mael-lukas/2425_Maker_MiniatureHomeControl/Media/Project pictures/pic2.jpeg

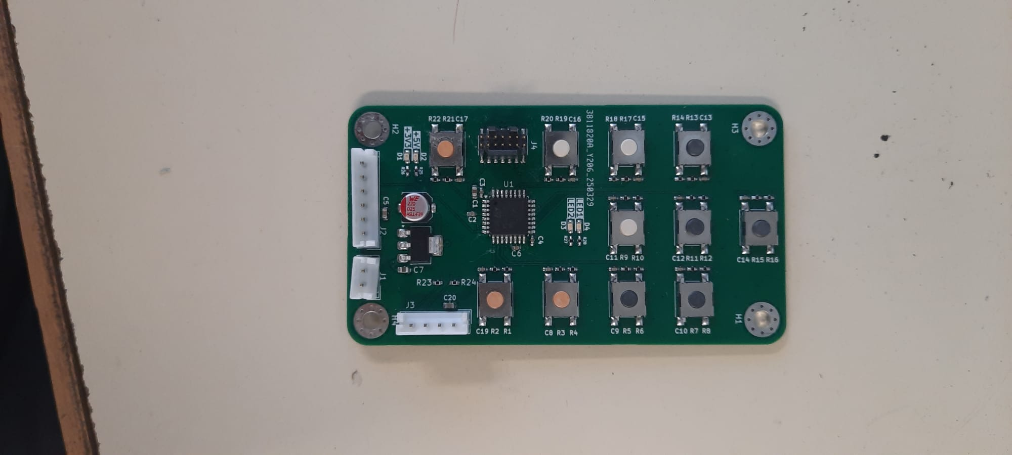
Media/Project pictures/pic2.jpeg
