mael-lukas/2425_Maker_MiniatureHomeControl/Media/Project pictures/pic14.png

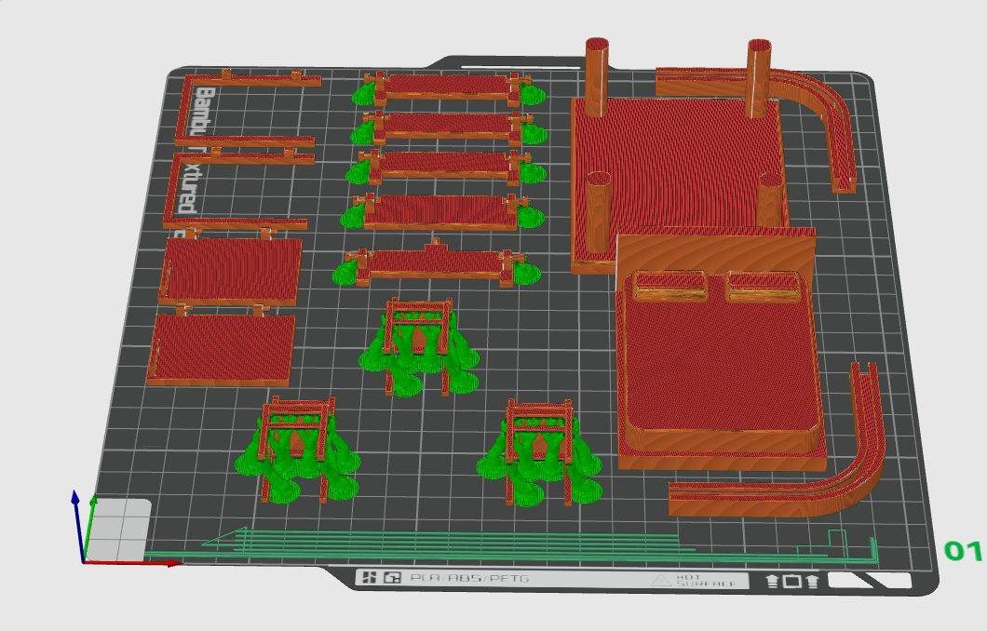
Media/Project pictures/pic14.png
