mael-lukas/2425_Maker_MiniatureHomeControl/Media/Project pictures/pic17.png

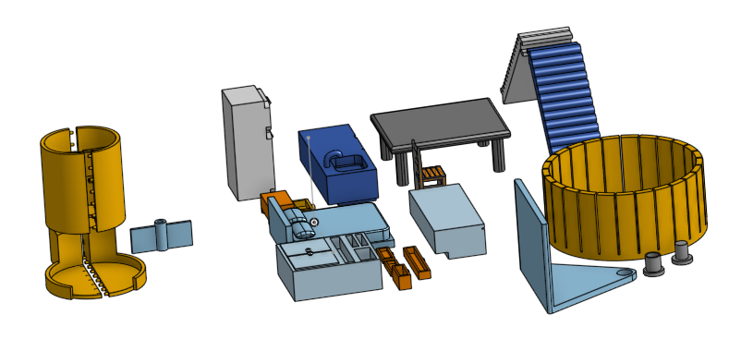
Media/Project pictures/pic17.png
