mael-lukas/2425_Maker_MiniatureHomeControl/Media/Project pictures/pic.jpeg

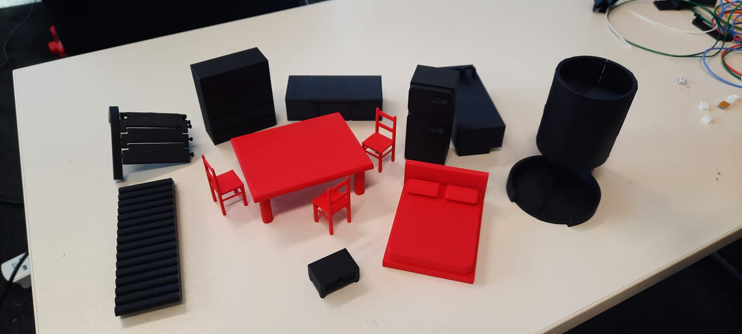
Media/Project pictures/pic.jpeg
