mael-lukas/2425_Maker_MiniatureHomeControl/Project Management/archi diagram.jpg

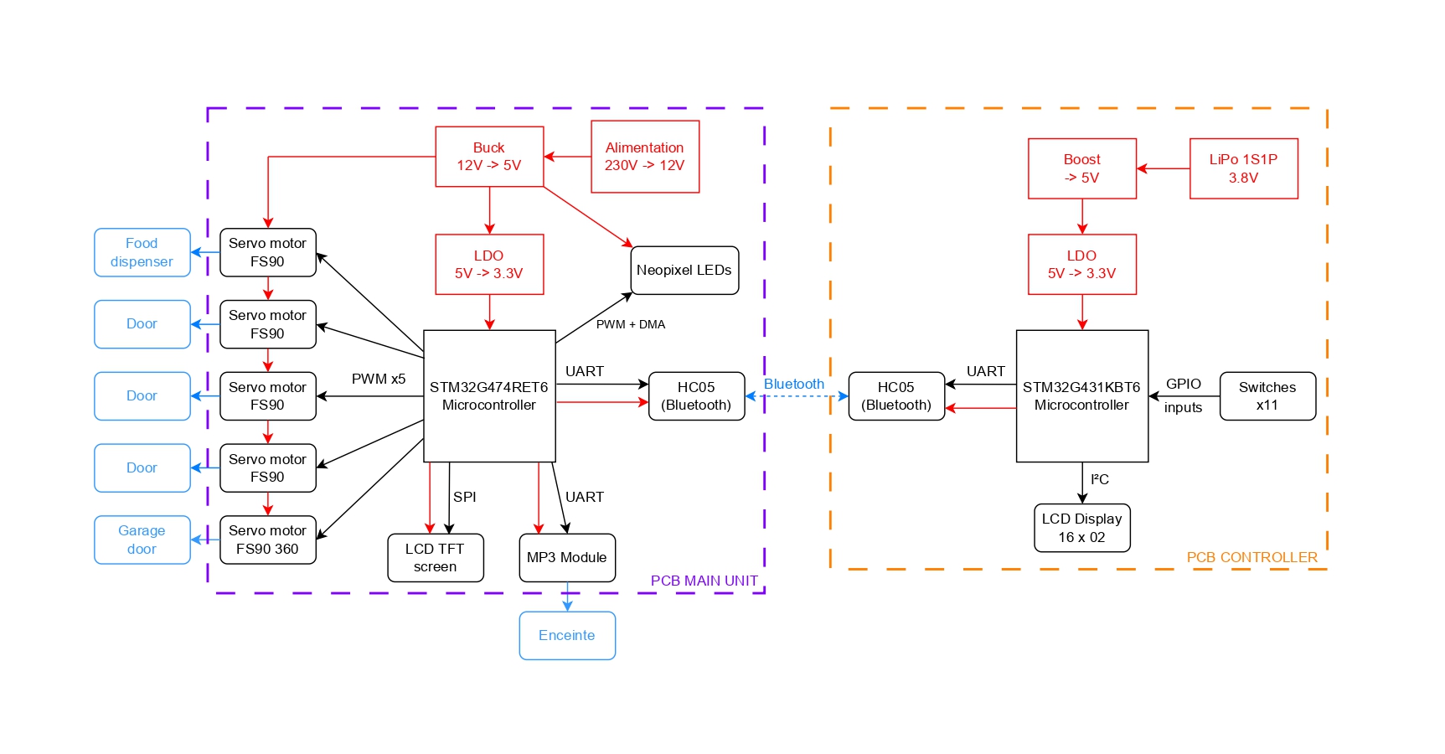
Project Management/archi diagram.jpg
