mael-lukas/2425_Maker_MiniatureHomeControl/CAD/food_3.stl

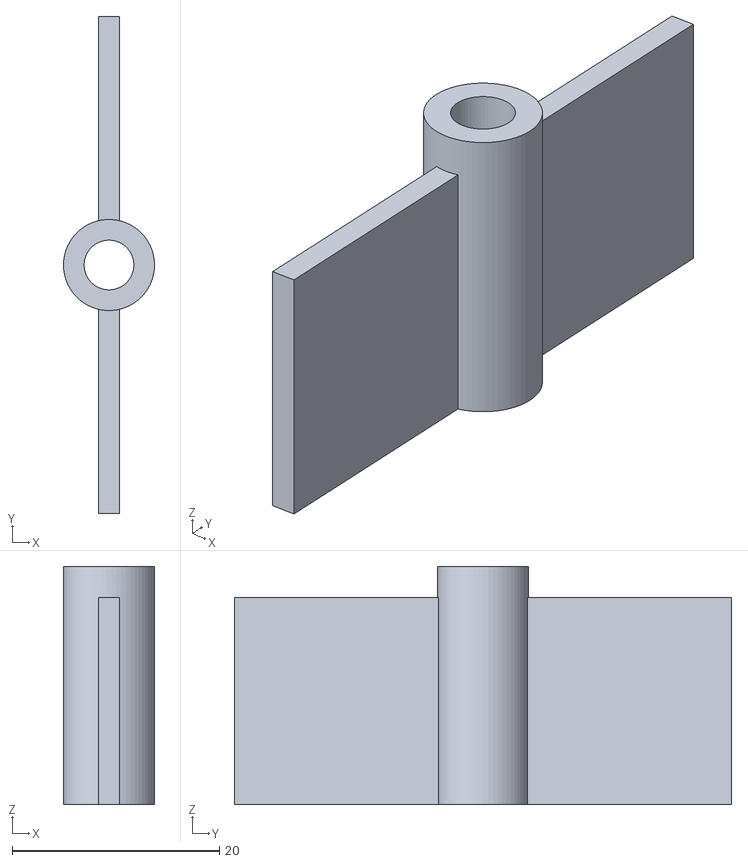
[picture p43: CAD file, 2025-04-19]
CAD/food_3.stl
8.80 x 48.0 x 23.0
