mael-lukas/2425_Maker_MiniatureHomeControl/CAD/door_1.stl

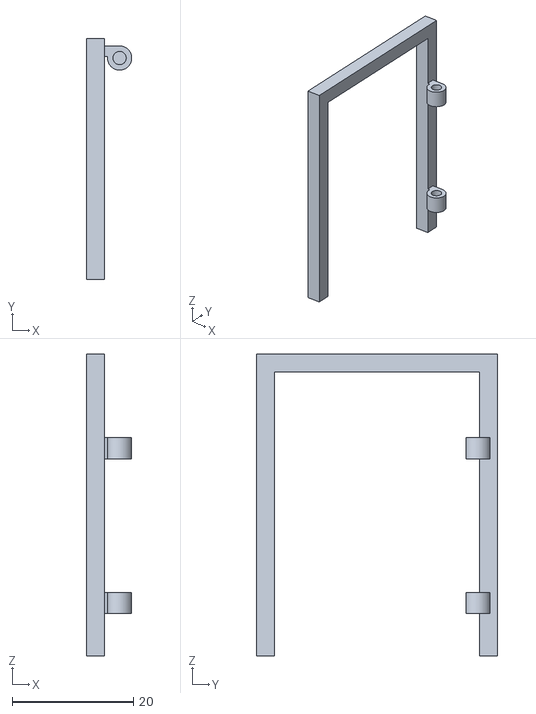
[picture p44: CAD file, 2025-04-19]
CAD/door_1.stl
7.50 x 39.8 x 49.8
