mael-lukas/2425_Maker_MiniatureHomeControl/CAD/gdoor_3.stl

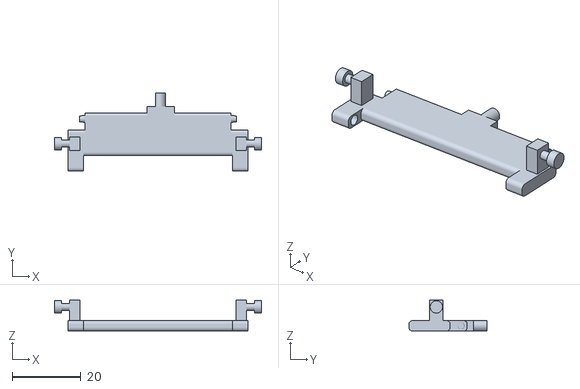
[picture p45: CAD file, 2025-04-19]
CAD/gdoor_3.stl
60.3 x 22.8 x 9.00
