mael-lukas/2425_Maker_MiniatureHomeControl/CAD/stairs_1.stl

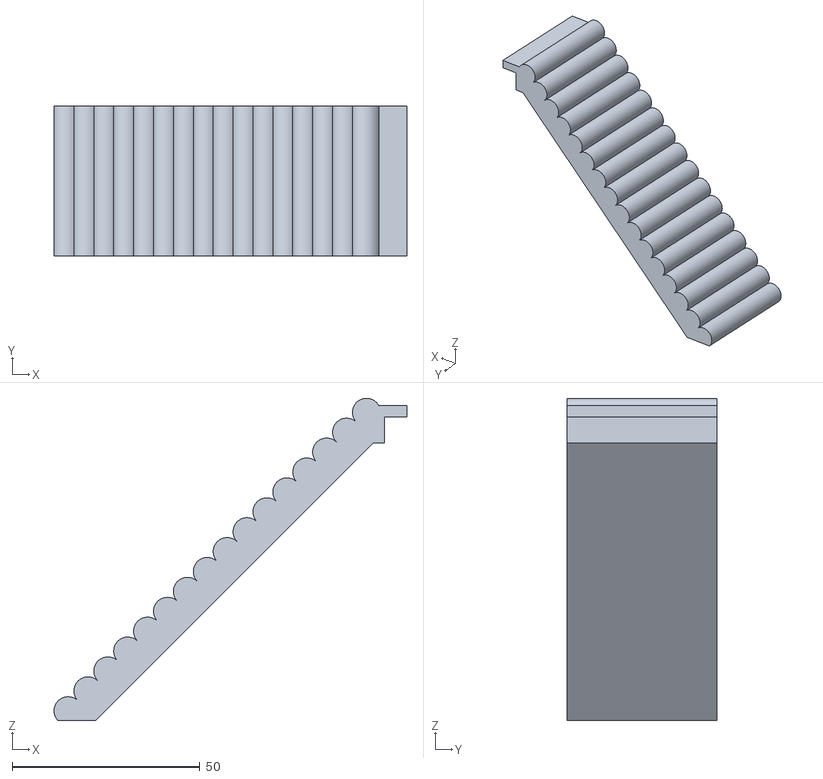
[picture p46: CAD file, 2025-04-19]
CAD/stairs_1.stl
94.1 x 40.0 x 85.9
