mael-lukas/2425_Maker_MiniatureHomeControl/CAD/door_2.stl

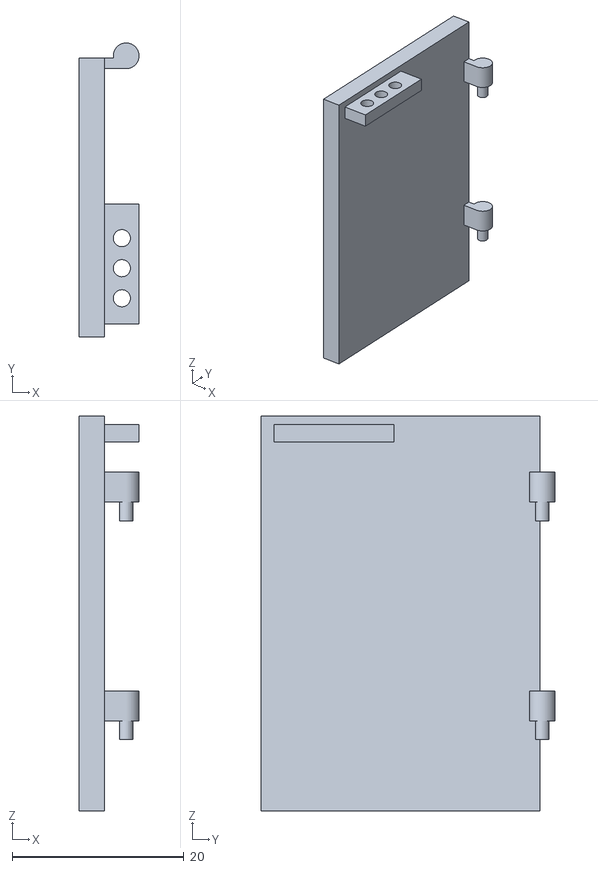
[picture p47: CAD file, 2025-04-19]
CAD/door_2.stl
7.00 x 34.2 x 46.0
