mael-lukas/2425_Maker_MiniatureHomeControl/CAD/rail_1.stl

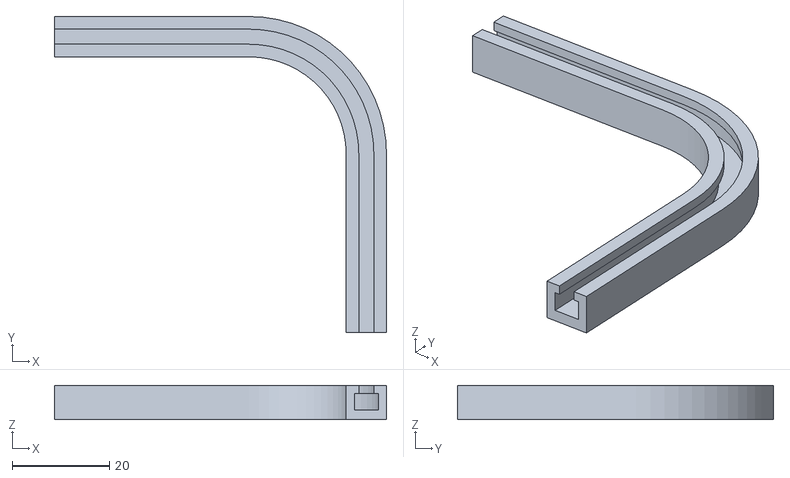
[picture p48: CAD file, 2025-04-19]
CAD/rail_1.stl
68.3 x 65.0 x 7.00
