mael-lukas/2425_Maker_MiniatureHomeControl/CAD/gdoor_1.stl

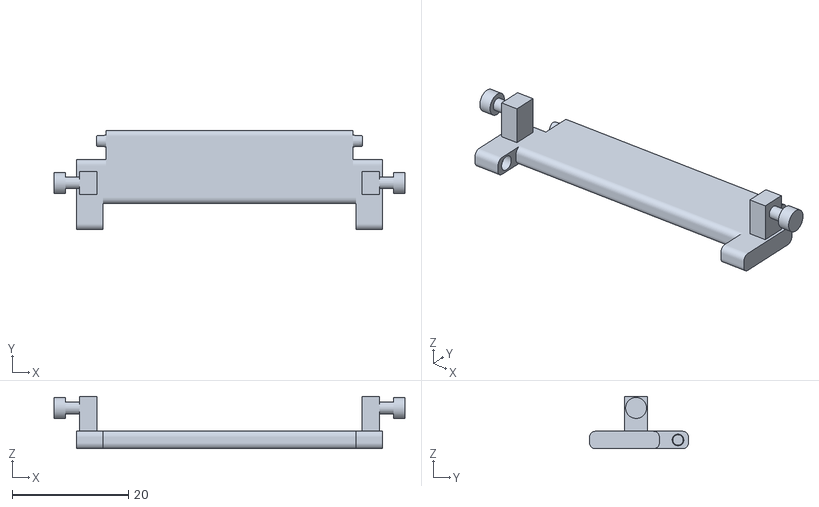
[picture p49: CAD file, 2025-04-19]
CAD/gdoor_1.stl
60.3 x 17.0 x 9.00
