mael-lukas/2425_Maker_MiniatureHomeControl/CAD/drawer_1.stl

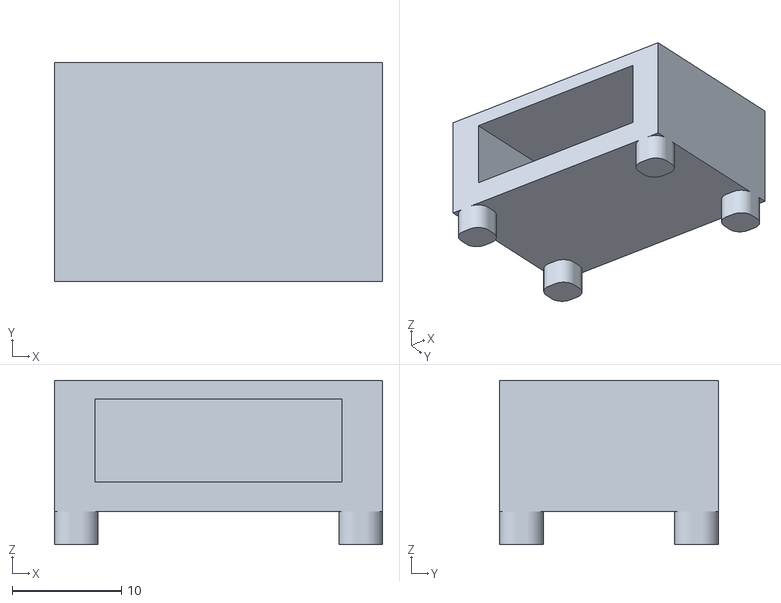
[picture p50: CAD file, 2025-04-19]
CAD/drawer_1.stl
30.0 x 20.0 x 15.0
