mael-lukas/2425_Maker_MiniatureHomeControl/CAD/table.stl

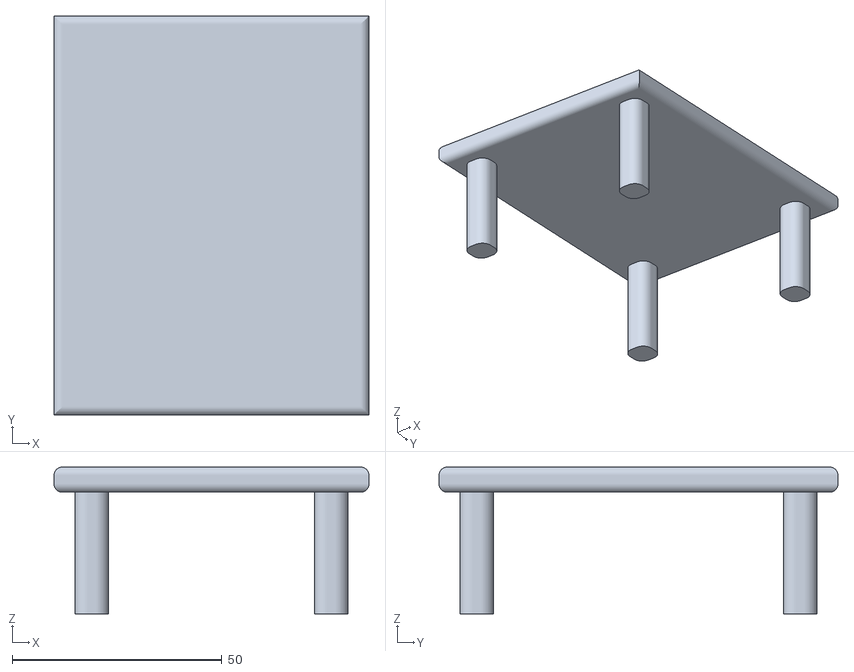
[picture p51: CAD file, 2025-04-19]
CAD/table.stl
75.0 x 95.0 x 35.0
