mael-lukas/2425_Maker_MiniatureHomeControl/Software/Maker_MiniatureHomeControl/Core/Inc/servos.h

/*
 * servos.h
 *
 *  Created on: Apr 7, 2025
 *      Author: administrateur
 */

#ifndef INC_SERVOS_H_
#define INC_SERVOS_H_

#include "main.h"

typedef struct h_servo_struct {
	TIM_HandleTypeDef *timer;
	uint32_t timerChannel;
	uint16_t pos0;
	uint16_t pos1;
	int currentPos;
} h_servo_t;

void servoInit(h_servo_t *servoHandle, TIM_HandleTypeDef *timer, uint32_t timerChannel);
void turnServo(h_servo_t *servoHandle);

#endif /* INC_SERVOS_H_ */
